Alan-Lomax/RFID_NFC_TAG_9x6/Datasheets/Blank Smith Chart Alternate Style.jpg

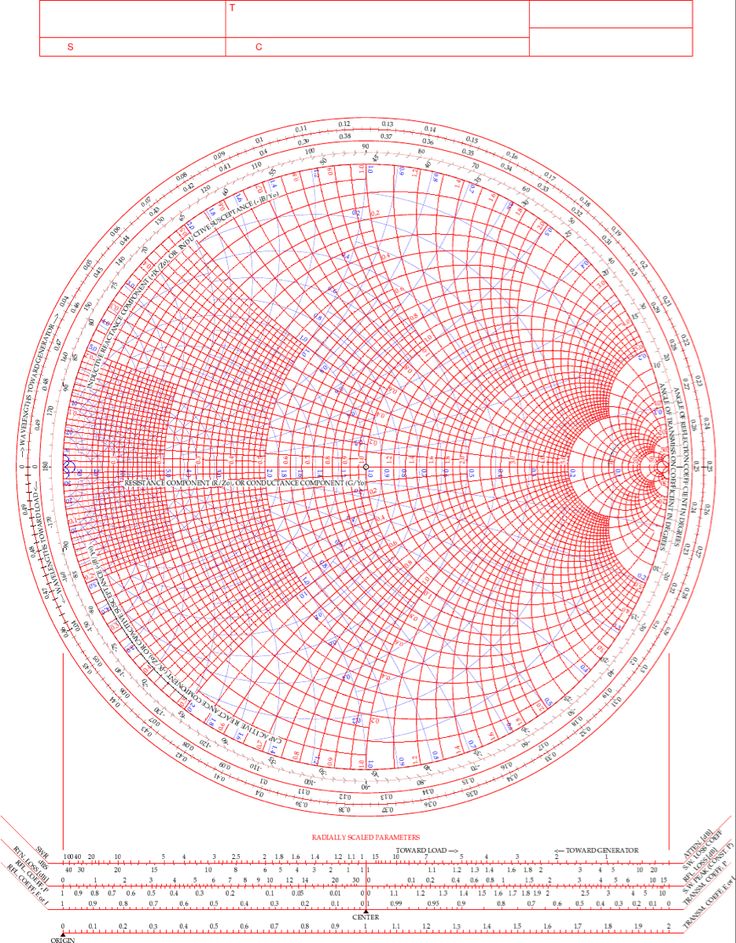
Datasheets/Blank Smith Chart Alternate Style.jpg
