Alan-Lomax/RFID_NFC_TAG_9x6/Invoices/01 Copy of Invoice with part numbers (redacted).jpg

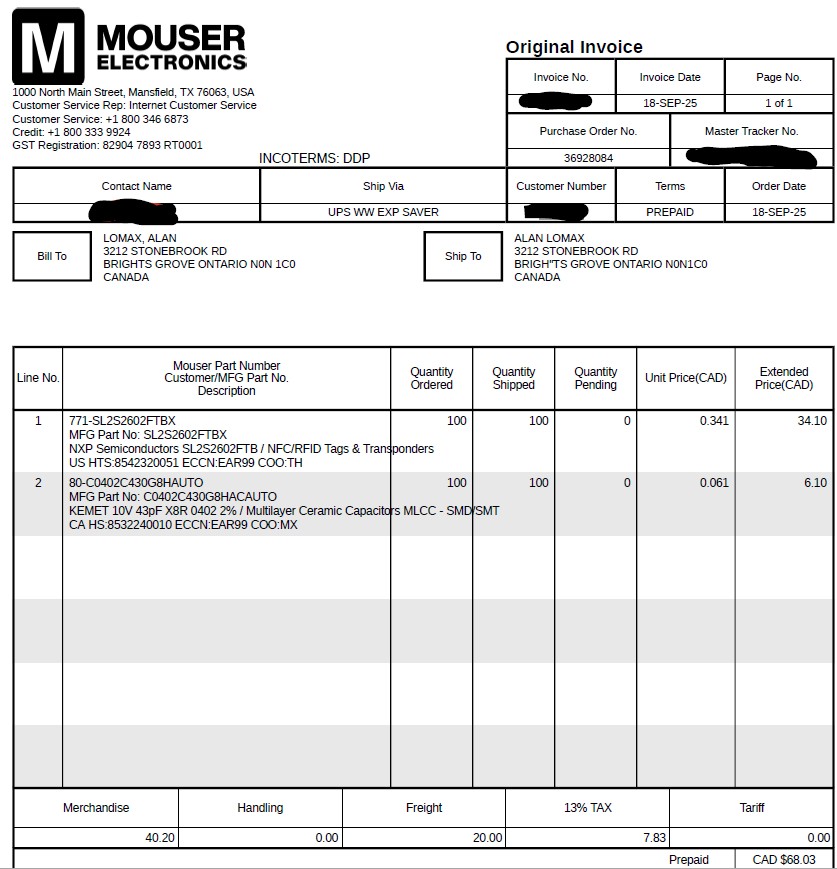
Invoices/01 Copy of Invoice with part numbers (redacted).jpg
