Alan-Lomax/RFID_NFC_TAG_9x6/Photos and testing/02 Overview of board on hot plate during warm up to 100 Deg C all parts are present .JPG

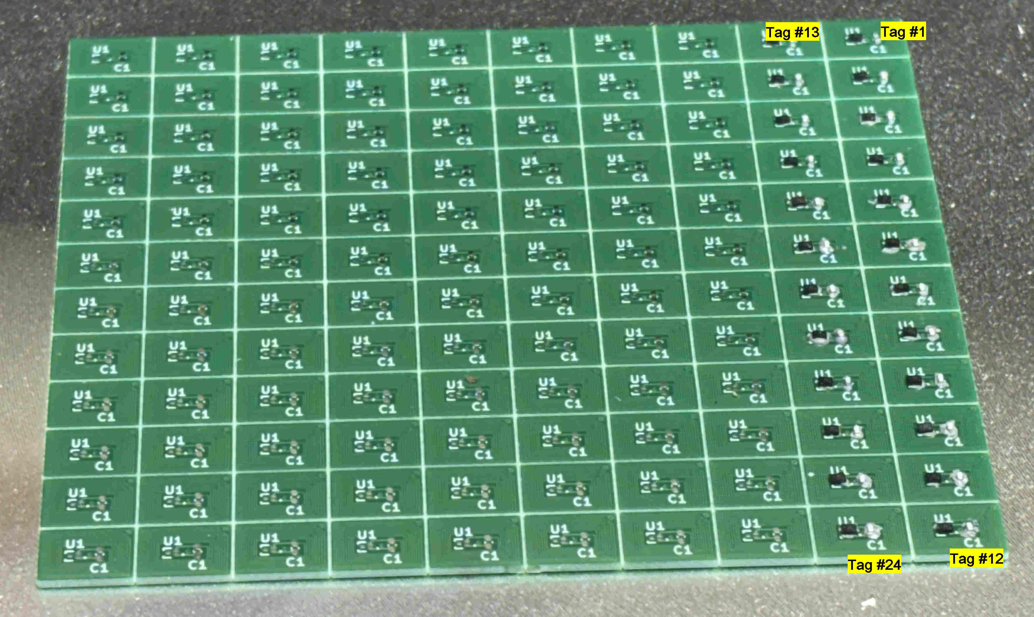
Photos and testing/02 Overview of board on hot plate during warm up to 100 Deg C all parts are present .JPG
