Alan-Lomax/RFID_NFC_TAG_9x6/Photos and testing/95 Murata purchased 3mm RFID Tag all in one.jpg

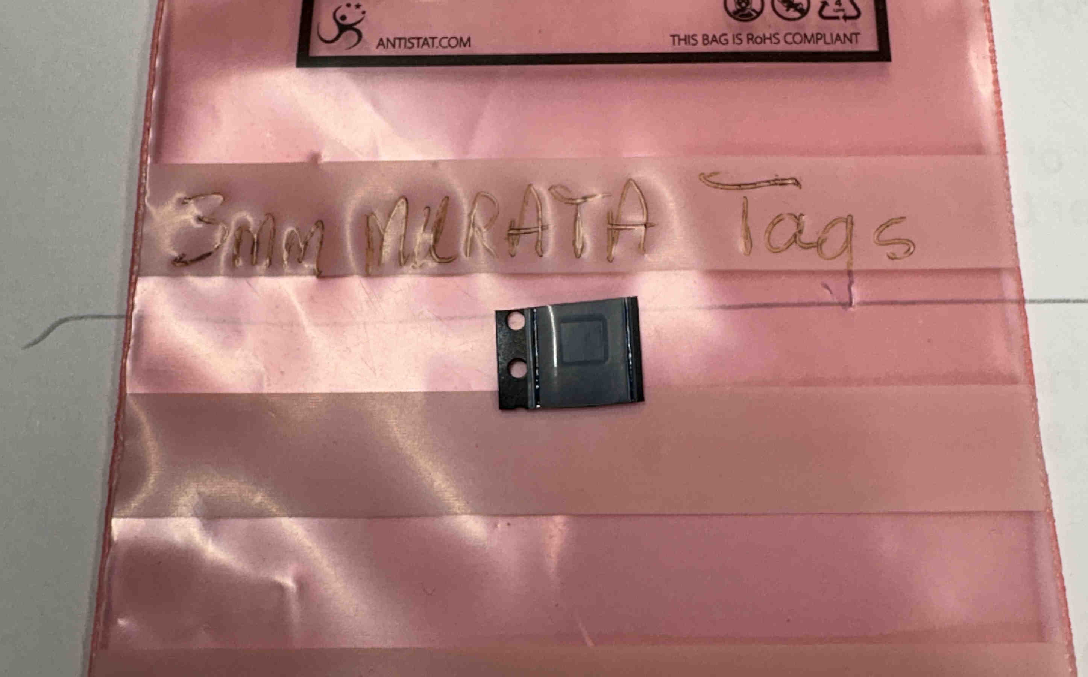
Photos and testing/95 Murata purchased 3mm RFID Tag all in one.jpg
