Alan-Lomax/RFID_NFC_TAG_9x6/Photos and testing/00 PCBs Arrived - shown as received fresh out of the package IMG_8032.JPG

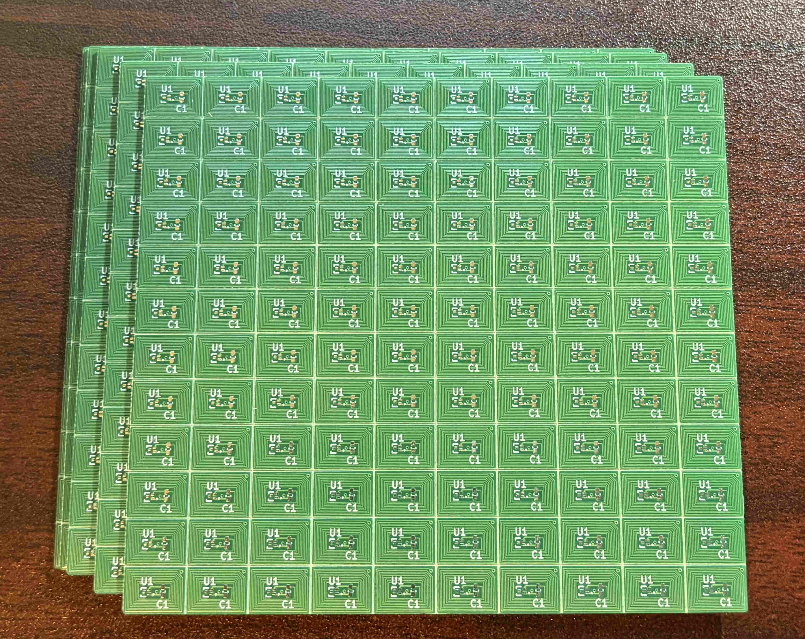
Photos and testing/00 PCBs Arrived - shown as received fresh out of the package IMG_8032.JPG
