Alan-Lomax/RFID_NFC_TAG_9x6/Photos and testing/06 Each tag was held in front of the StarfishRail aerial for a quick go no-go test IMG_8048.JPG

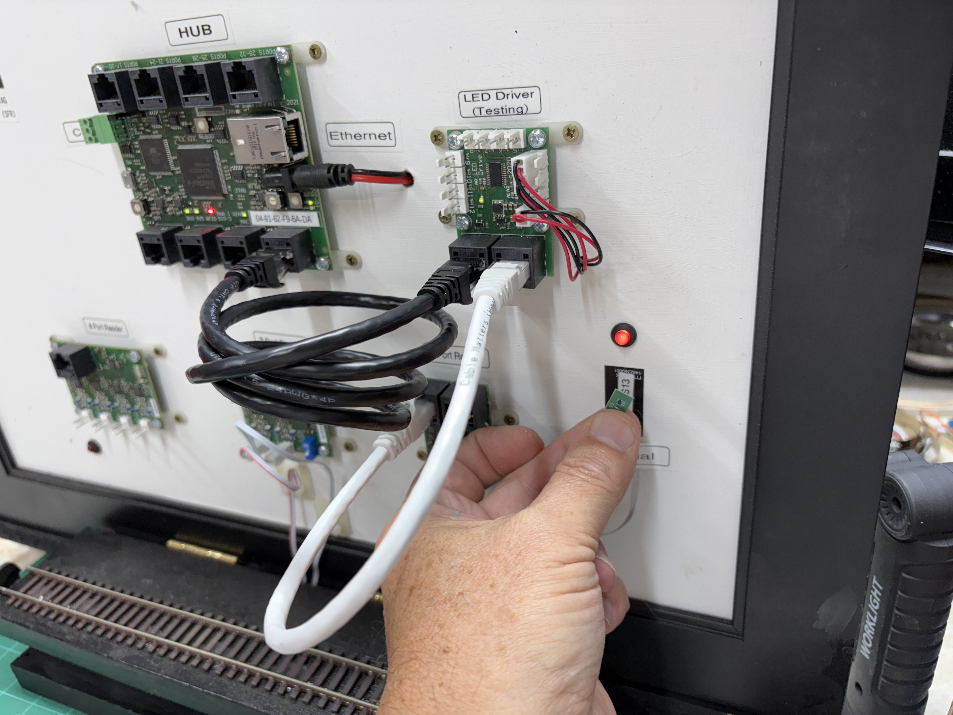
Photos and testing/06 Each tag was held in front of the StarfishRail aerial for a quick go no-go test IMG_8048.JPG
