Alan-Lomax/RFID_NFC_TAG_9x6/Photos and testing/10 Pleasantly suprised 20 of 24 tags passed IMG_8047.JPG

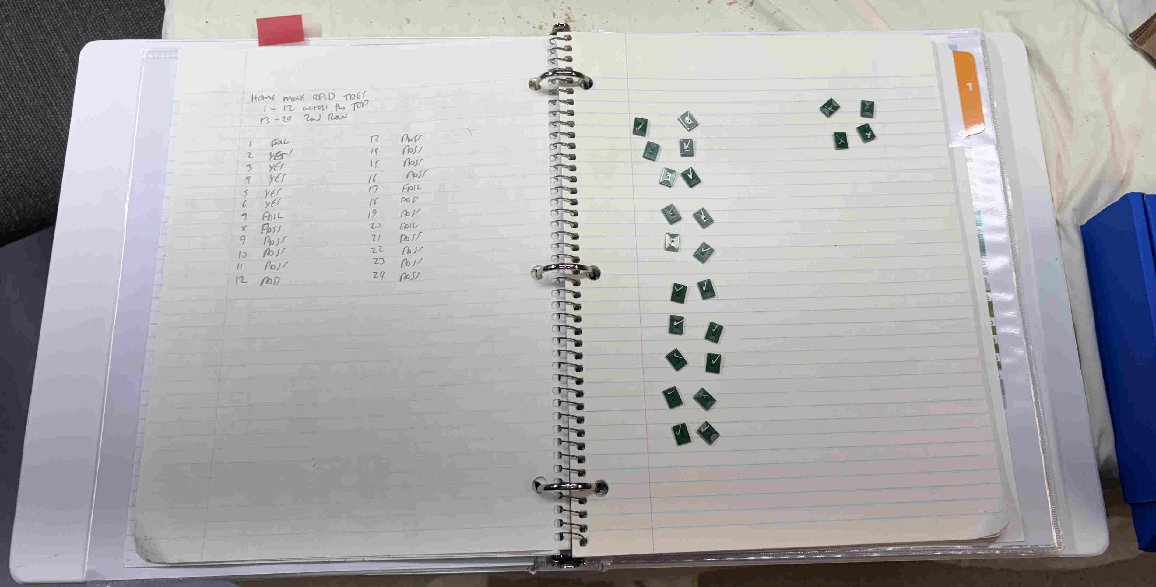
Photos and testing/10 Pleasantly suprised 20 of 24 tags passed IMG_8047.JPG
