Alan-Lomax/RFID_NFC_TAG_9x6/Photos and testing/20 Test Wagon with SFR Tag and my design shown loose beside it for comparison IMG_8050.JPG

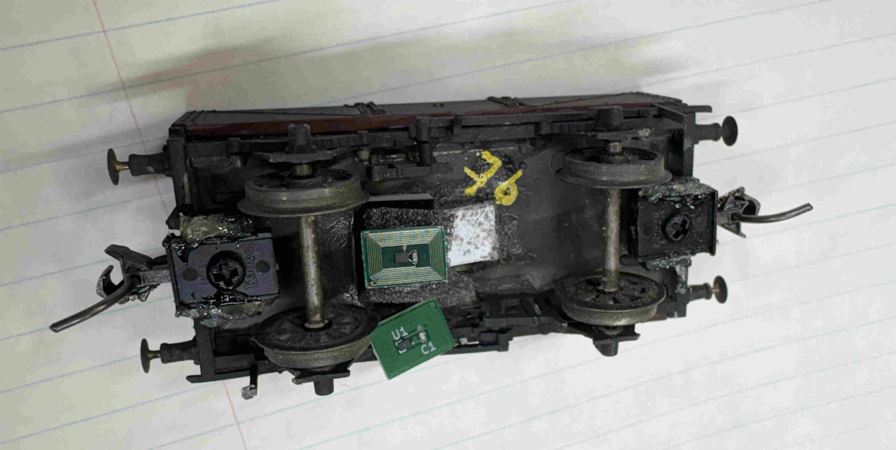
Photos and testing/20 Test Wagon with SFR Tag and my design shown loose beside it for comparison IMG_8050.JPG
