Alan-Lomax/RFID_NFC_TAG_9x6/Photos and testing/90 A sense of scale - the fine tweezer is pointing to the removed RFID chip.jpg

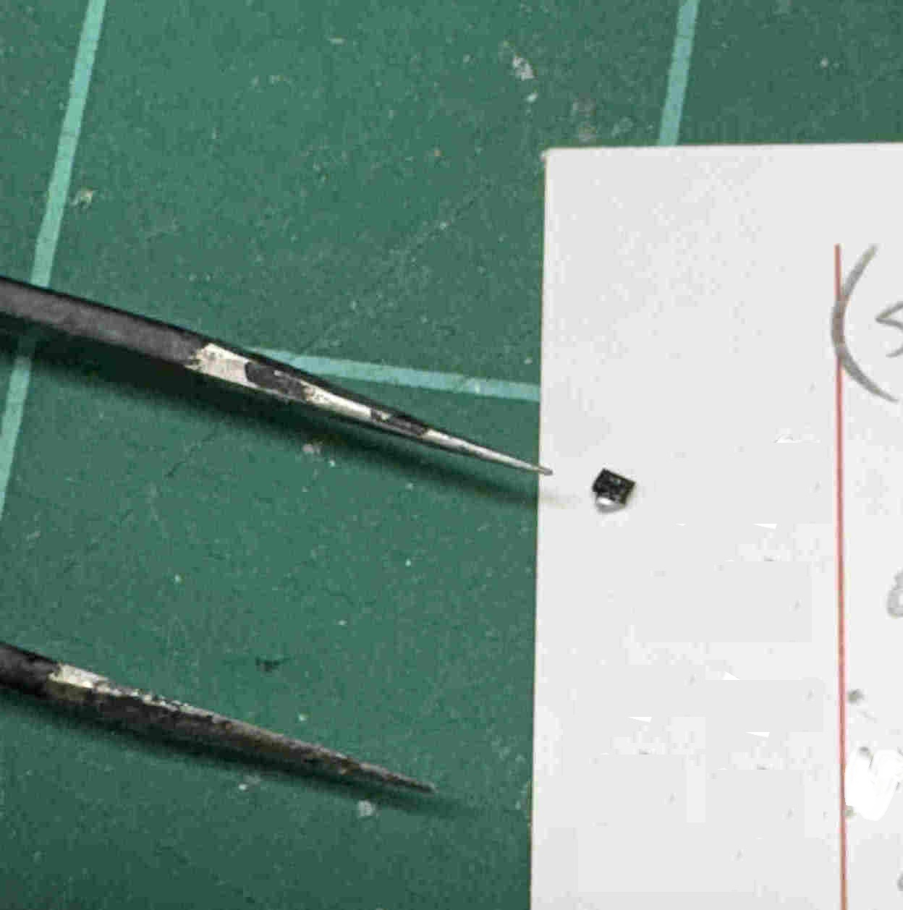
Photos and testing/90 A sense of scale - the fine tweezer is pointing to the removed RFID chip.jpg
