Alan-Lomax/RFID_NFC_TAG_9x6/Photos and testing/90 A sesne of scale - the tweezer is pointing to the removed RFID chip from 20 IMG_8045.JPG

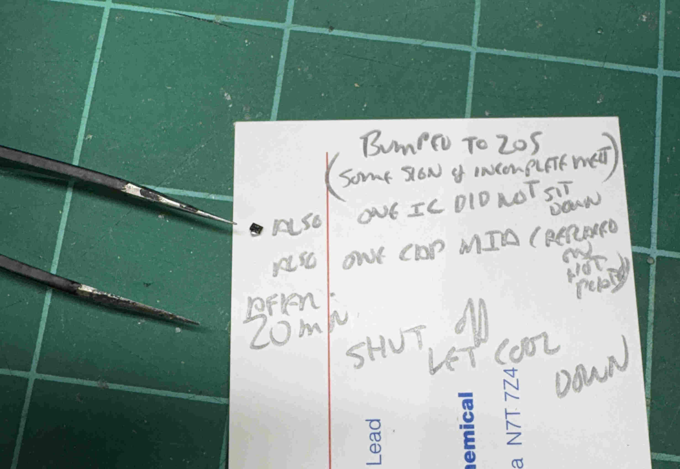
Photos and testing/90 A sesne of scale - the tweezer is pointing to the removed RFID chip from 20 IMG_8045.JPG
