Alan-Lomax/RFID_NFC_TAG_9x6/Photos and testing/93 showing successful read at 28mm.jpg

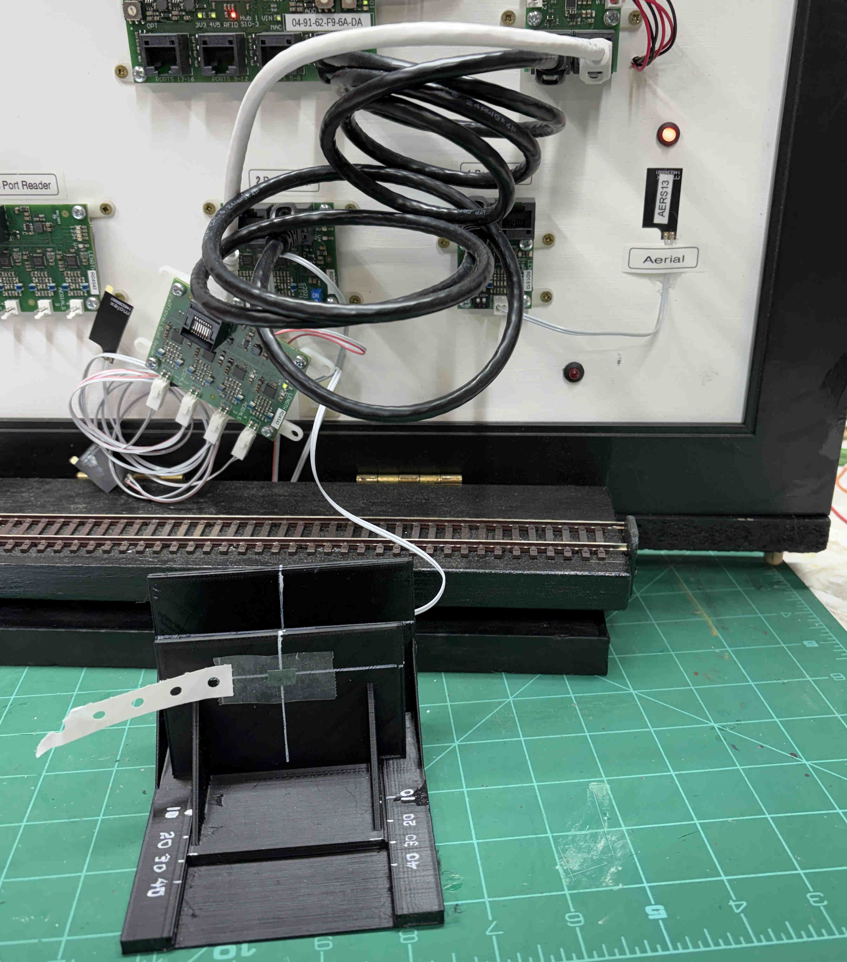
Photos and testing/93 showing successful read at 28mm.jpg
