Alan-Lomax/RFID_NFC_TAG_9x6/KiCad Files/RFID_NFC_TAG_9x6.kicad_sch

## KiCad design KiCad Files/RFID_NFC_TAG_9x6.kicad_sch (2025-12-10)

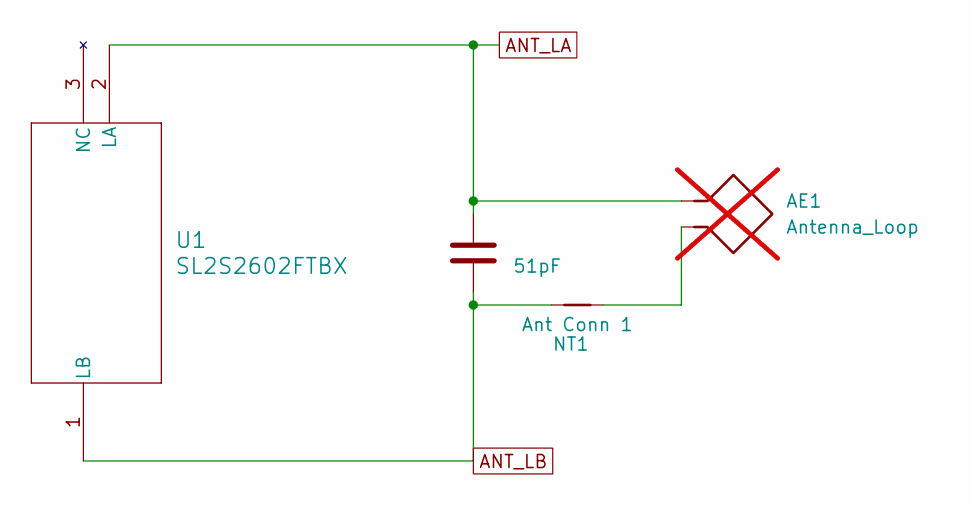
[picture p28: schematic RFID_NFC_TAG_9x6.kicad_sch]

Parts:
AE1: Antenna_Loop; not fitted
C1: 51pF; C_0402_1005Metric_Pad0.74x0.62mm_HandSolder
NT1: Ant Conn 1; NetTie-2_SMD_Pad0.5mm
U1: SL2S2602FTBX; XSON3_SL2S2602_NXP

Connections:
ANT_LA: AE1.1, C1.1, U1.2 (LA)
ANT_LB: C1.2, NT1.2, U1.1 (LB)
unnamed: AE1.2, NT1.1
