Alan-Lomax/RFID_NFC_TAG_9x6/Photos and testing/03 At some point tag 20 was flipped vertical and had to be removed. A new tag was fitted from the tape IMG_8043.JPG

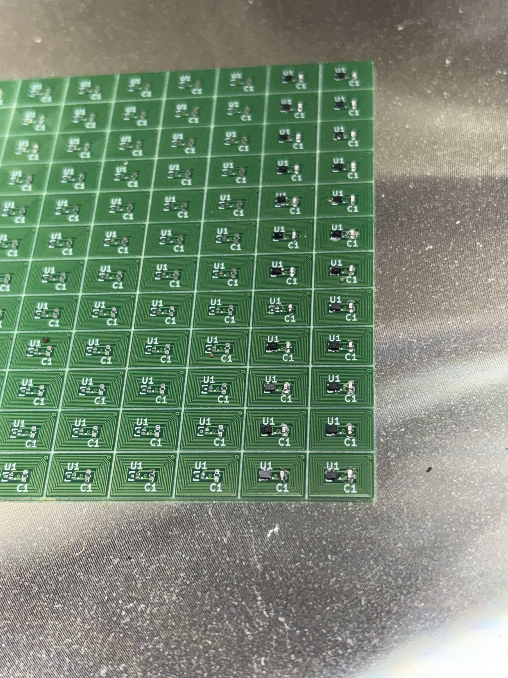
Photos and testing/03 At some point tag 20 was flipped vertical and had to be removed. A new tag was fitted from the tape IMG_8043.JPG
